edwardrousseau/ChristmasTreePCBTiny10/Images/front_kicad.png

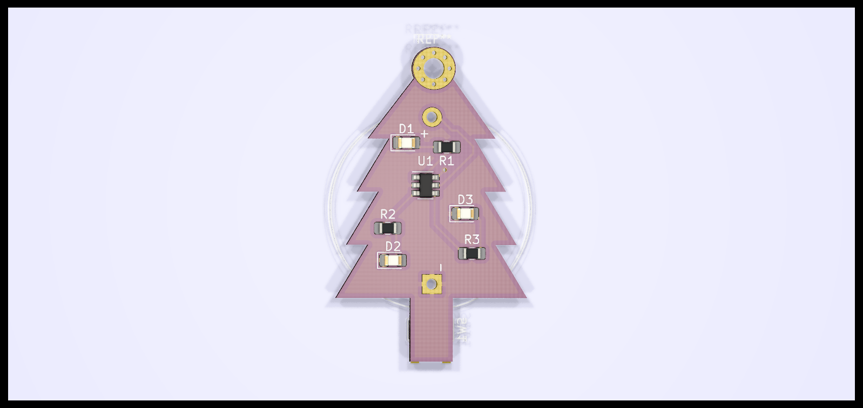
Images/front_kicad.png
